Lescurel/hop_lamp/hop_petal.scad

use <hop.scad>

s=0.05;
size_scale=s;
t=0;
angle_scale=t;
plywood=4*0.9;

hjortron_scale(115*(1.-size_scale*angle_scale),p=plywood);
