Lescurel/hop_lamp/top_plate.scad

use <hop.scad>

projection()
rotate([0,90,0])
top_plate(p=4*0.9);
